Giuseppe34/Projekt_fabscan/fritzing/Výstřižek3.PNG

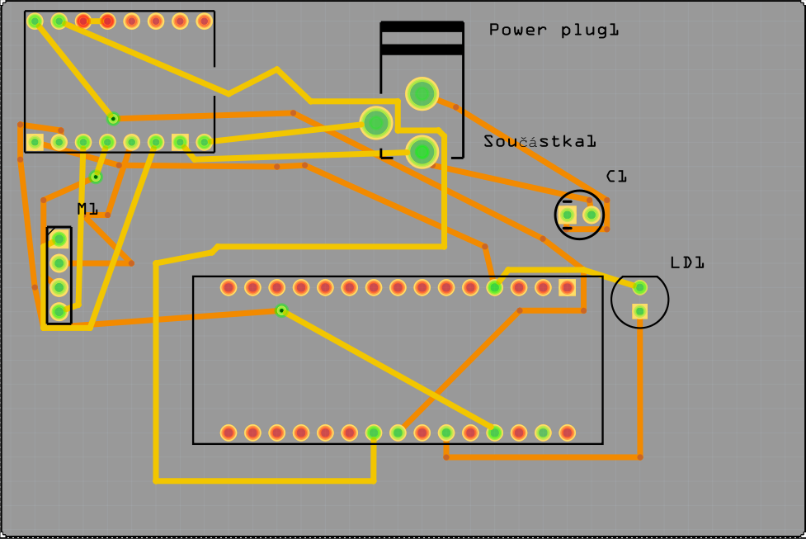
fritzing/Výstřižek3.PNG
