Giuseppe34/Projekt_fabscan/zaznamy/49332815_308379026550463_6107267839339528192_n.jpg

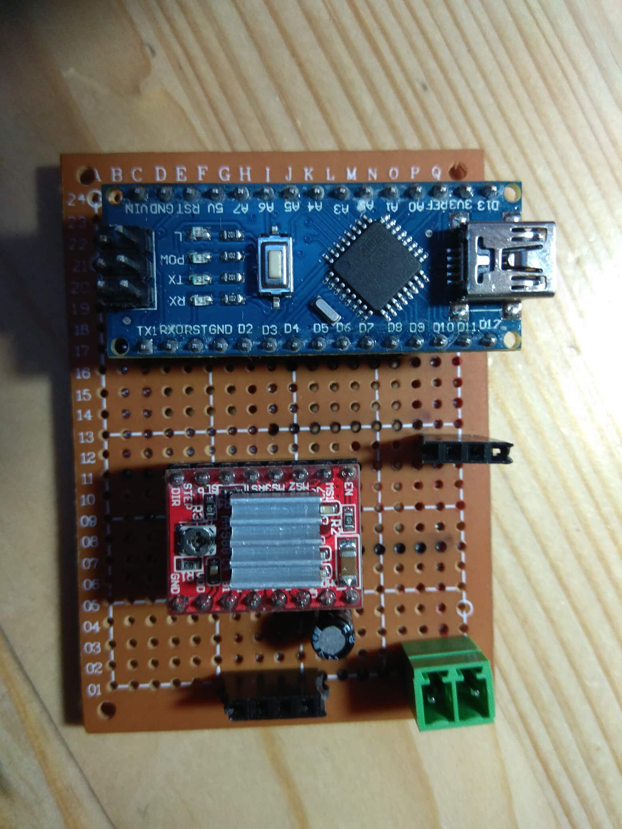
zaznamy/49332815_308379026550463_6107267839339528192_n.jpg
