Giuseppe34/Projekt_fabscan/zaznamy/IMG_20181010_145559.jpg

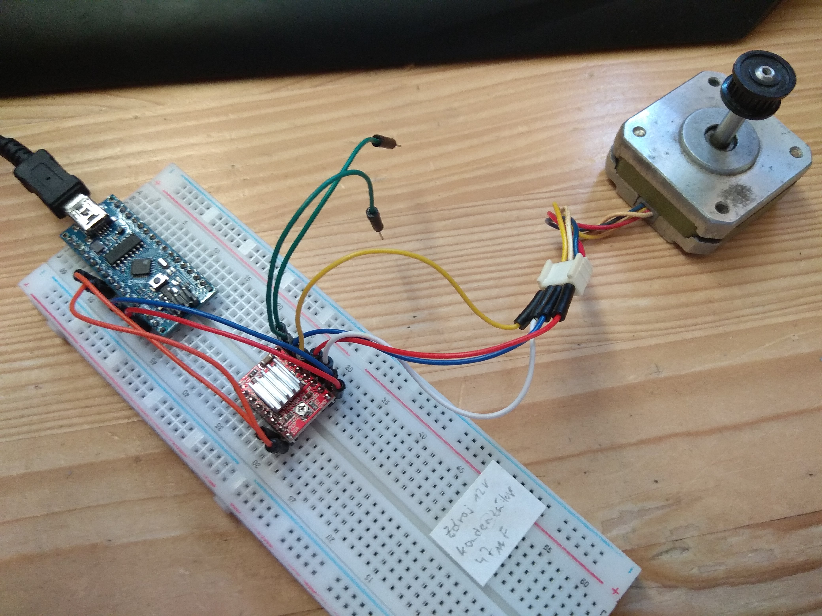
zaznamy/IMG_20181010_145559.jpg
