Giuseppe34/Projekt_fabscan/zaznamy/linelasr.jpg

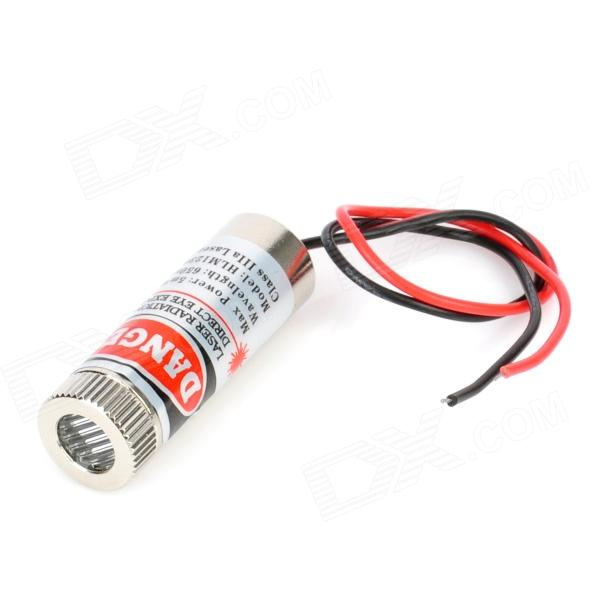
zaznamy/linelasr.jpg
