Giuseppe34/Projekt_fabscan/zaznamy/Screenshot from 2019-01-06 20_04_07.png

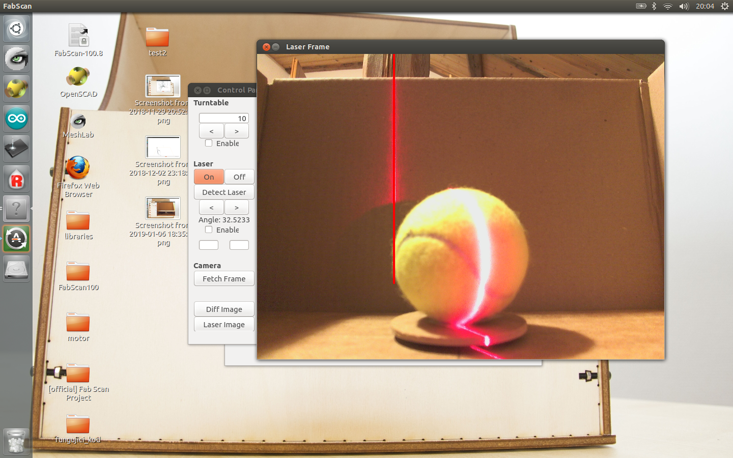
zaznamy/Screenshot from 2019-01-06 20_04_07.png
