Giuseppe34/Projekt_fabscan/zaznamy/Screenshot from 2019-01-06 20_10_37 (1).png

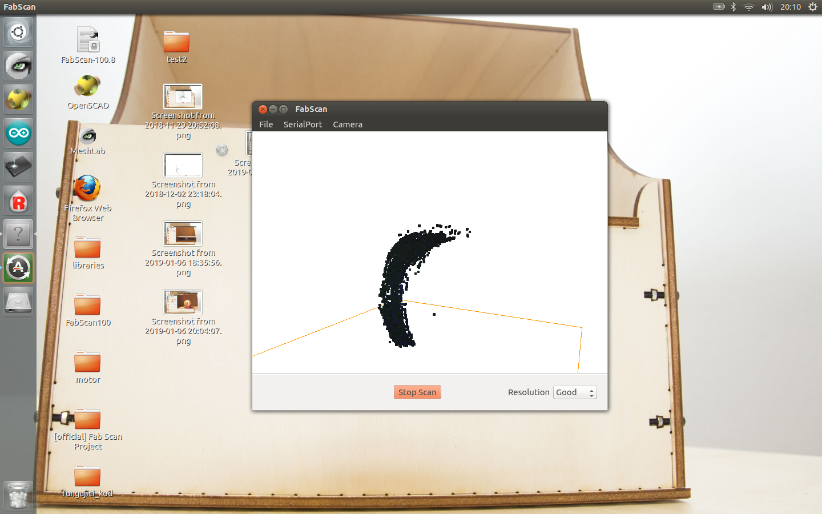
zaznamy/Screenshot from 2019-01-06 20_10_37 (1).png
