Giuseppe34/Projekt_fabscan/zaznamy/Screenshot from 2019-01-08 18_28_43.png

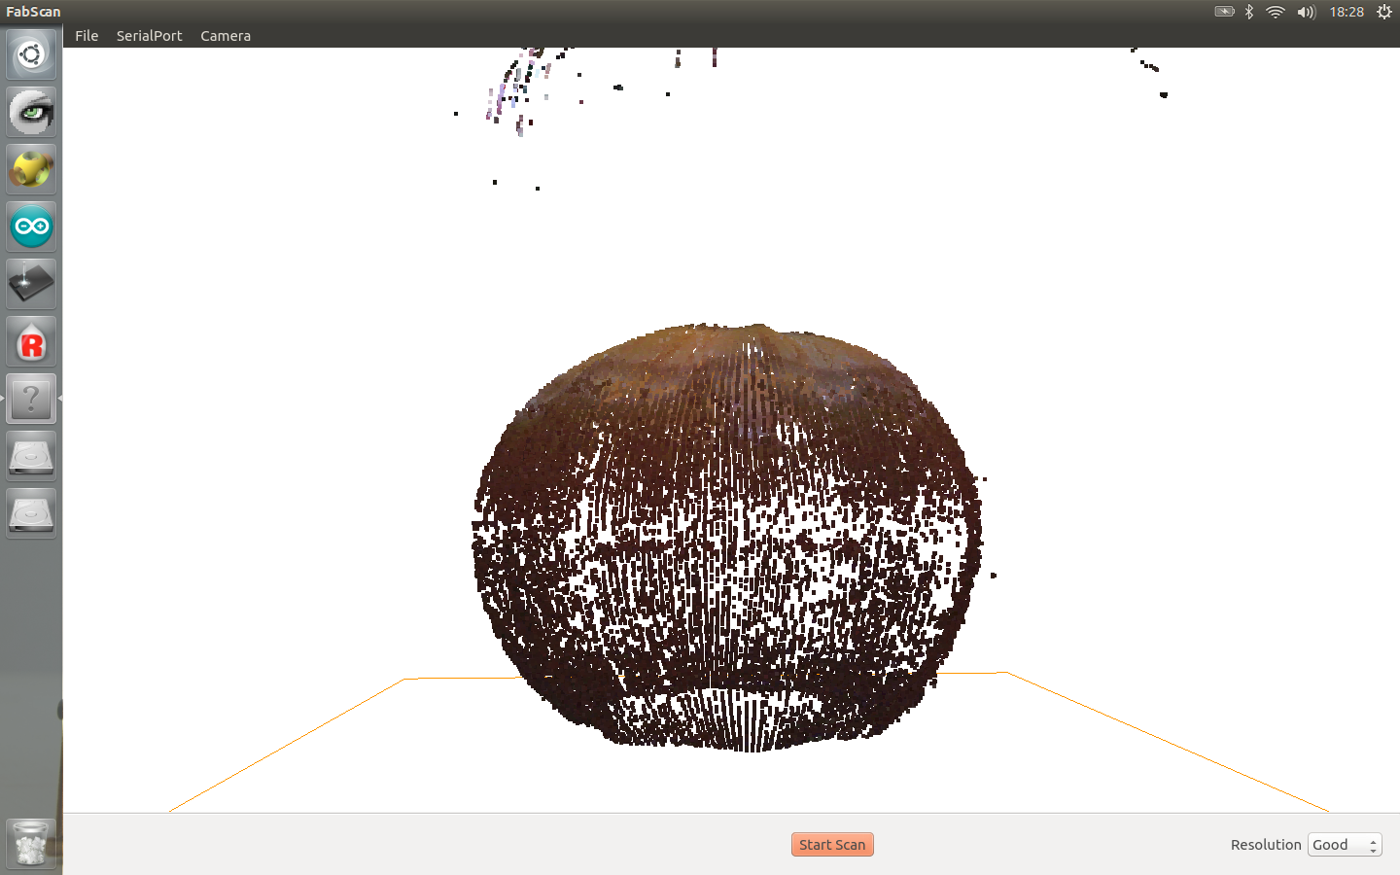
zaznamy/Screenshot from 2019-01-08 18_28_43.png
