Giuseppe34/Projekt_fabscan/zaznamy/Screenshot from 2019-01-08 18_37_41.png

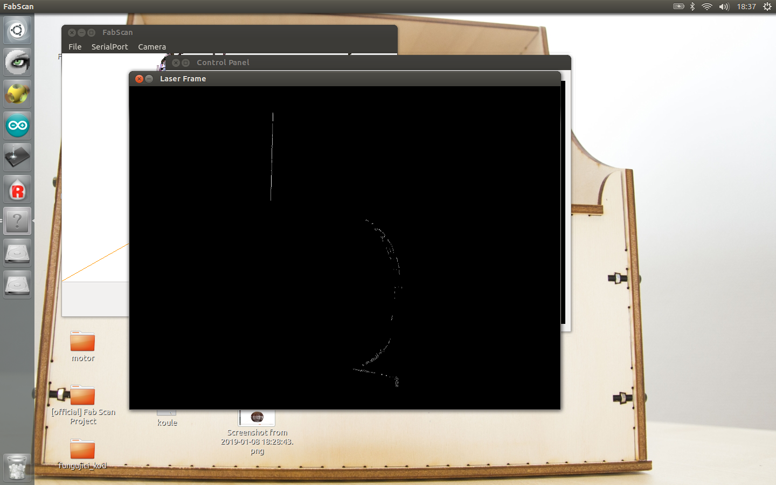
zaznamy/Screenshot from 2019-01-08 18_37_41.png
