Giuseppe34/Projekt_fabscan/zaznamy/Screenshot from 2019-01-08 19_11_59.png

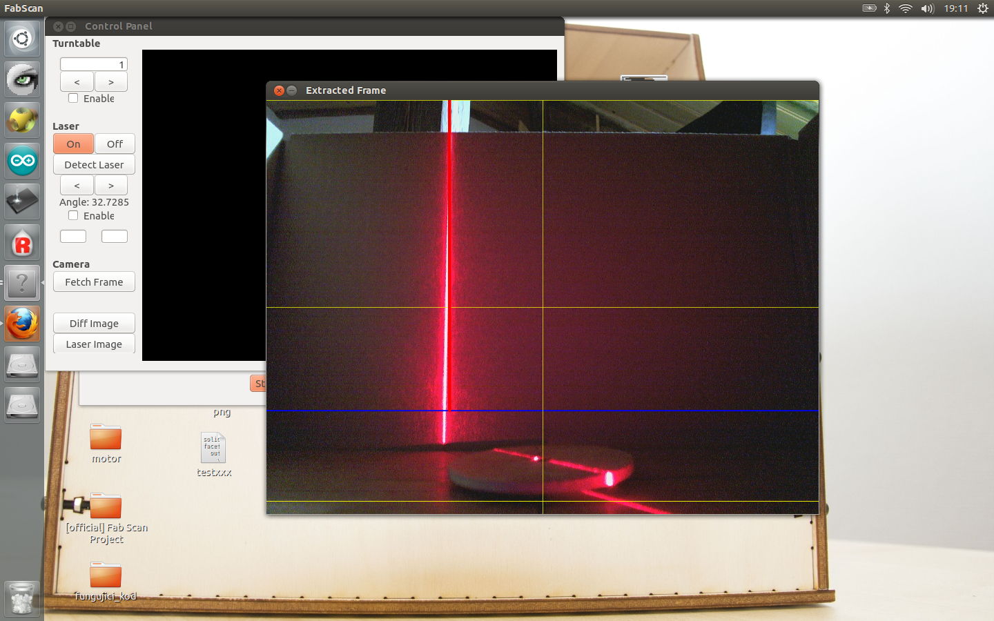
zaznamy/Screenshot from 2019-01-08 19_11_59.png
