Giuseppe34/Projekt_fabscan/zaznamy/Výstřižek2.PNG

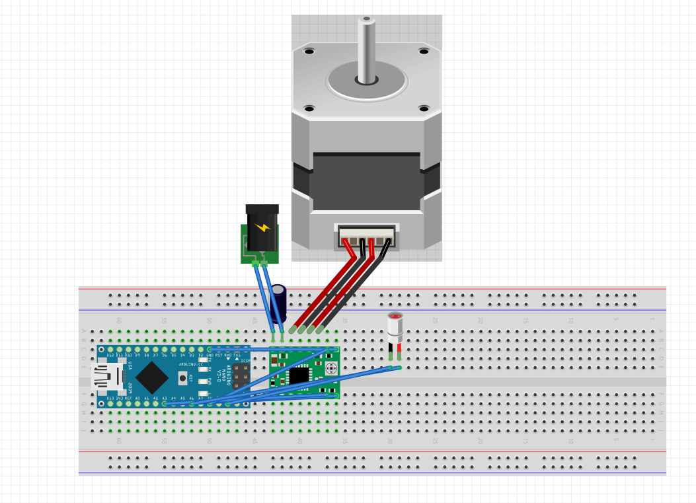
zaznamy/Výstřižek2.PNG
