Giuseppe34/Projekt_fabscan/zaznamy/Výstřižek (1).PNG

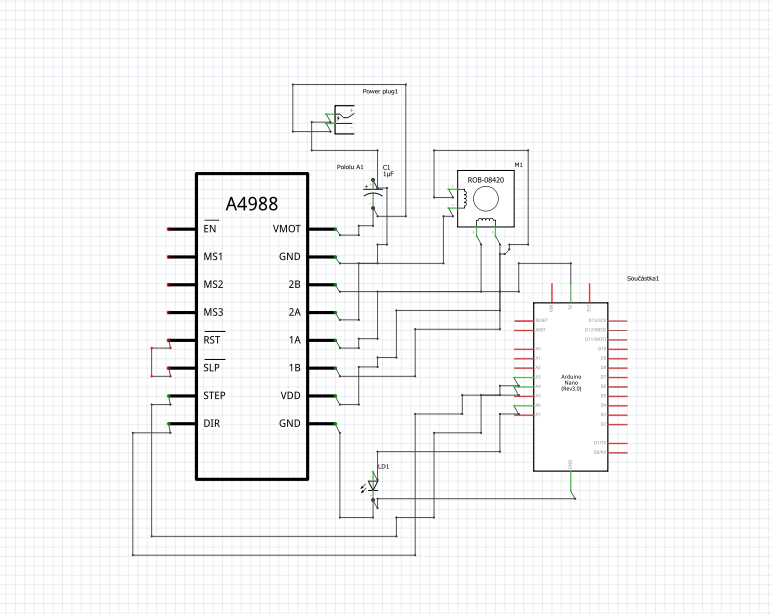
zaznamy/Výstřižek (1).PNG
