Giuseppe34/Projekt_fabscan/fritzing/schema_etch_silk_bottom.pdf

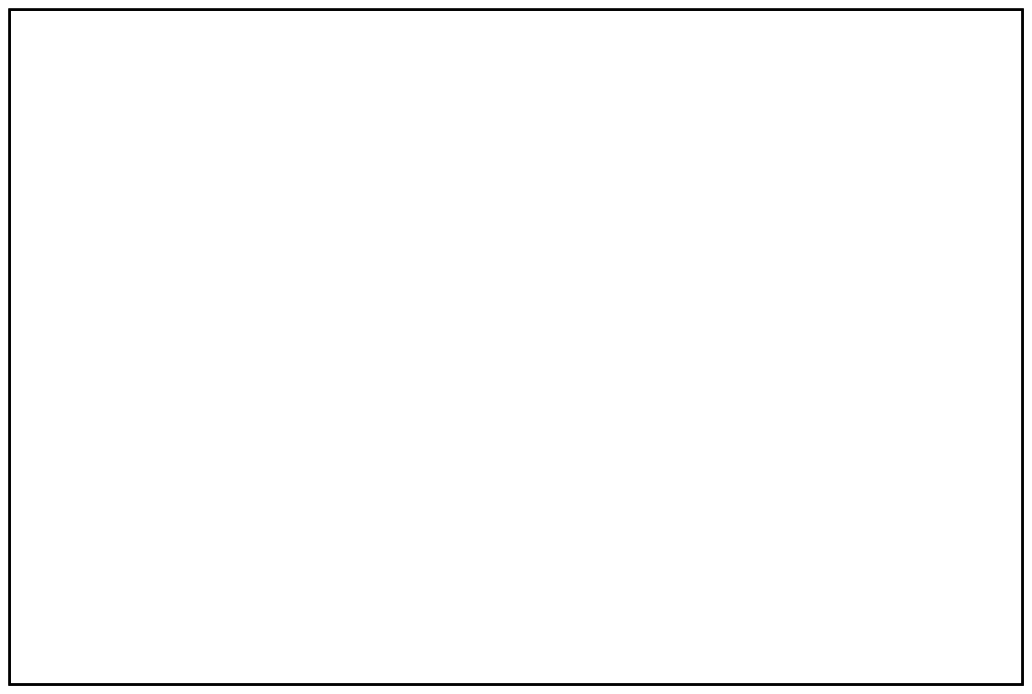
[picture p36: page 1]
