Giuseppe34/Projekt_fabscan/fritzing/schema_etch_silk_top.pdf

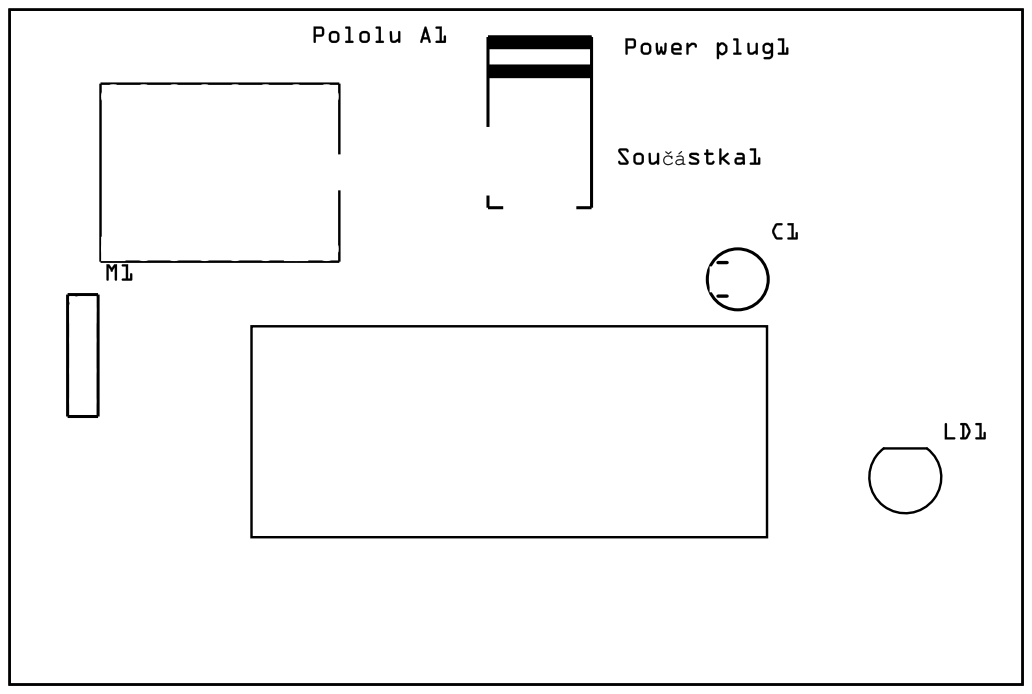
[picture p37: page 1]
