Giuseppe34/Projekt_fabscan/fritzing/schema_etch_silk_top_mirror.pdf

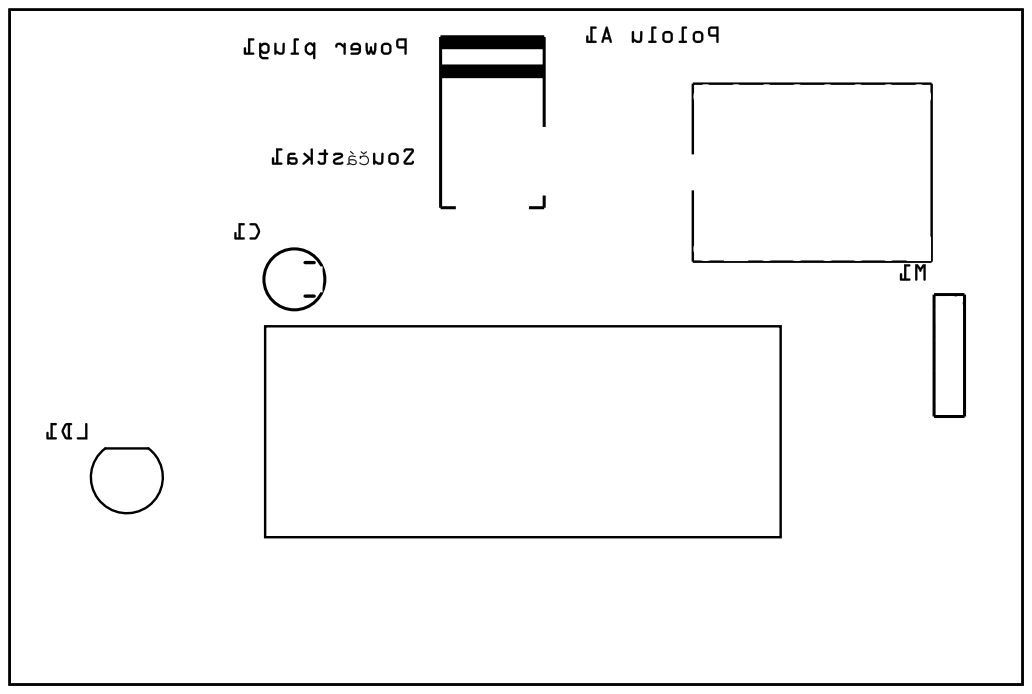
[picture p38: page 1]
