Giuseppe34/Projekt_fabscan/krokovyradic/krokovyradic.kicad_pcb

## KiCad design esp32-daq-board/cta.kicad_pcb


Parts:
ADC1, ADC2, ADC3, ADC4: MCP3208; DIP-16_W7.62mm_LongPads
CTA1, CTA2, CTA3, CTA4: Conn_01x09; PinHeader_1x09_P2.54mm_Vertical
CV51: 100n; C_Rect_L7.2mm_W3.0mm_P5.00mm_FKS2_FKP2_MKS2_MKP2
CV52: 100u; CP_Radial_D6.3mm_P2.50mm
CVDD1, CVDD2, CVDD3, CVDD4: 100n; C_Rect_L7.2mm_W3.0mm_P5.00mm_FKS2_FKP2_MKS2_MKP2
CVR1, CVR2, CVR3, CVR4: 100n; C_Rect_L7.2mm_W3.0mm_P5.00mm_FKS2_FKP2_MKS2_MKP2
CVREF1: 1u; CP_Radial_D4.0mm_P2.00mm
Dref1, Dref2: 1N4148; D_DO-35_SOD27_P7.62mm_Horizontal
J2, J3: Conn_01x15_Female; PinSocket_1x15_P2.54mm_Vertical
JREF1: Conn_01x03; TerminalBlock_bornier-3_P5.08mm
RVref1: R_POT; Potentiometer_Bourns_3296W_Vertical
Rref1: 2.5k; R_Axial_DIN0207_L6.3mm_D2.5mm_P10.16mm_Horizontal
UVref1: LM336; TO-92L_Inline_Wide

Connections:
/CLK: ADC1.13 (CLK), ADC2.13 (CLK), ADC3.13 (CLK), ADC4.13 (CLK), J3.7
/CS1: ADC1.10 (~CS~/SHDN), J3.8
/CS2: ADC2.10 (~CS~/SHDN), J3.2
/CS3: ADC3.10 (~CS~/SHDN), J2.8
/CS4: ADC4.10 (~CS~/SHDN), J2.9
/MISO: ADC1.12 (Dout), ADC2.12 (Dout), ADC3.12 (Dout), ADC4.12 (Dout), J3.6
/MOSI: ADC1.11 (Din), ADC2.11 (Din), ADC3.11 (Din), ADC4.11 (Din), J3.1
/VDD: ADC1.16 (Vdd), ADC2.16 (Vdd), ADC3.16 (Vdd), ADC4.16 (Vdd), CV51.2, CV52.2, CVDD1.2, CVDD2.2, CVDD3.2, CVDD4.2, J2.15, JREF1.1, Rref1.2
/Vref: ADC1.15 (Vref), ADC2.15 (Vref), ADC3.15 (Vref), ADC4.15 (Vref), CVR1.2, CVR2.2, CVR3.2, CVR4.2, CVREF1.1, Dref1.2 (A), JREF1.3, Rref1.1, UVref1.2 (V+)
GND: ADC1.9 (DGND), ADC1.14 (AGND), ADC2.9 (DGND), ADC2.14 (AGND), ADC3.9 (DGND), ADC3.14 (AGND), ADC4.9 (DGND), ADC4.14 (AGND), CTA1.1, CTA2.1, CTA3.1, CTA4.1, CV51.1, CV52.1, CVDD1.1, CVDD2.1, CVDD3.1, CVDD4.1, CVR1.1, CVR2.1, CVR3.1, CVR4.1, CVREF1.2, Dref2.1 (K), J2.14, JREF1.2, UVref1.3 (V-)
unnamed: ADC1.1 (CH0), CTA1.2
unnamed: ADC1.2 (CH1), CTA1.3
unnamed: ADC1.3 (CH2), CTA1.4
unnamed: ADC1.4 (CH3), CTA1.5
unnamed: ADC1.5 (CH4), CTA1.6
unnamed: ADC1.6 (CH5), CTA1.7
unnamed: ADC1.7 (CH6), CTA1.8
unnamed: ADC1.8 (CH7), CTA1.9
unnamed: ADC2.1 (CH0), CTA2.2
unnamed: ADC2.2 (CH1), CTA2.3
unnamed: ADC2.3 (CH2), CTA2.4
unnamed: ADC2.4 (CH3), CTA2.5
unnamed: ADC2.5 (CH4), CTA2.6
unnamed: ADC2.6 (CH5), CTA2.7
unnamed: ADC2.7 (CH6), CTA2.8
unnamed: ADC2.8 (CH7), CTA2.9
unnamed: ADC3.1 (CH0), CTA3.2
unnamed: ADC3.2 (CH1), CTA3.3
unnamed: ADC3.3 (CH2), CTA3.4
unnamed: ADC3.4 (CH3), CTA3.5
unnamed: ADC3.5 (CH4), CTA3.6
unnamed: ADC3.6 (CH5), CTA3.7
unnamed: ADC3.7 (CH6), CTA3.8
unnamed: ADC3.8 (CH7), CTA3.9
unnamed: ADC4.1 (CH0), CTA4.2
unnamed: ADC4.2 (CH1), CTA4.3
unnamed: ADC4.3 (CH2), CTA4.4
unnamed: ADC4.4 (CH3), CTA4.5
unnamed: ADC4.5 (CH4), CTA4.6
unnamed: ADC4.6 (CH5), CTA4.7
unnamed: ADC4.7 (CH6), CTA4.8
unnamed: ADC4.8 (CH7), CTA4.9
unnamed: Dref1.1 (K), RVref1.1
unnamed: Dref2.2 (A), RVref1.3
unnamed: RVref1.2, UVref1.1 (ADJ)


Board: 2 copper layers, 151.1 x 149.9 mm, 27 parts (0 on the bottom side), 45 nets.
